anikjain11/OpenDAQ-MixedSignal-AFE/Results/02_Schematics/csp_schematic.png

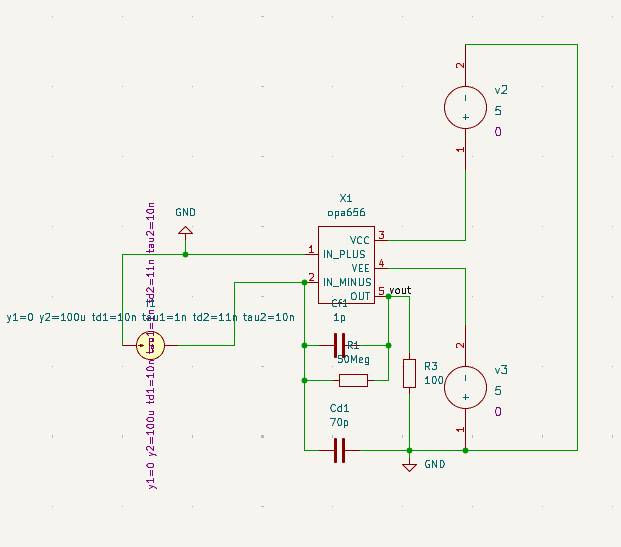
Results/02_Schematics/csp_schematic.png
