anikjain11/OpenDAQ-MixedSignal-AFE/Results/02_Schematics/Final_Schematic_Frontend.png

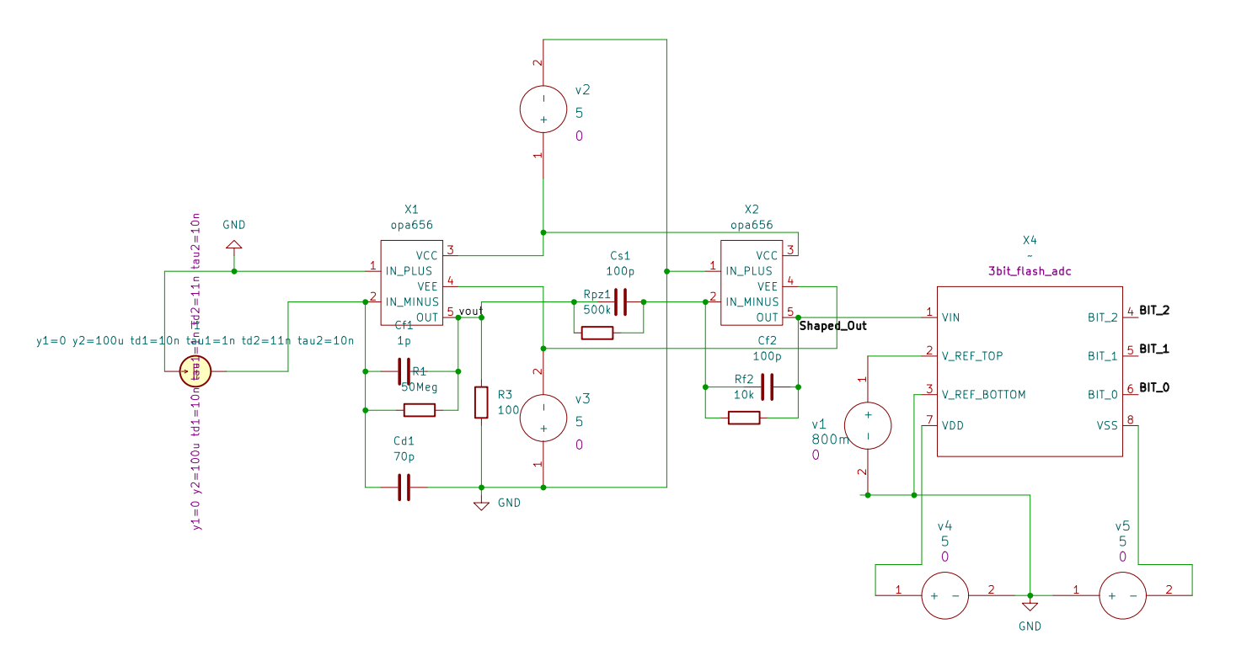
Results/02_Schematics/Final_Schematic_Frontend.png
