anikjain11/OpenDAQ-MixedSignal-AFE/Results/01_Simulations/csp_transient_response_1pC.png

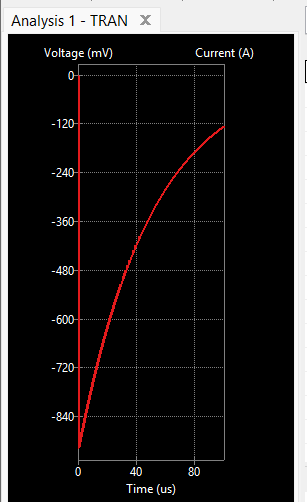
Results/01_Simulations/csp_transient_response_1pC.png
