anikjain11/OpenDAQ-MixedSignal-AFE/Results/01_Simulations/csp_transient_response_Shaped_Output.png

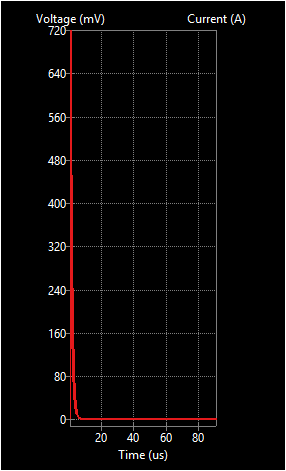
Results/01_Simulations/csp_transient_response_Shaped_Output.png
